solarkennedy/epaper-watch/Ubuntu_B7pt7b.h

const uint8_t Ubuntu_B7pt7bBitmaps[] PROGMEM = {
  0xFF, 0xF3, 0xF0, 0xDE, 0xF7, 0xB0, 0x1B, 0x0D, 0xBF, 0xFF, 0xF3, 0x61,
  0xB3, 0xFF, 0xFF, 0x6C, 0x36, 0x00, 0x30, 0xC7, 0xFF, 0xC3, 0x87, 0x87,
  0x0F, 0xFF, 0x8C, 0x30, 0x78, 0xCC, 0xD8, 0xCF, 0x8C, 0xF0, 0x7E, 0x00,
  0x7E, 0x0F, 0x31, 0xF3, 0x1B, 0x33, 0x1E, 0x38, 0x3E, 0x1B, 0x0D, 0x87,
  0x87, 0xDB, 0x3D, 0x9C, 0xFF, 0x3D, 0xC0, 0xFF, 0x27, 0x6E, 0xCC, 0xCC,
  0xCC, 0xE6, 0x72, 0x4E, 0x67, 0x33, 0x33, 0x33, 0x76, 0xE4, 0x25, 0x7E,
  0xED, 0xA8, 0x30, 0xCF, 0xFF, 0x30, 0xC0, 0x6D, 0xE0, 0xFF, 0xFF, 0x80,
  0x0C, 0x31, 0x86, 0x18, 0xC3, 0x0C, 0x31, 0x86, 0x18, 0xC3, 0x00, 0x39,
  0xEC, 0xF3, 0xCF, 0x3C, 0xF3, 0x79, 0xE0, 0x1B, 0xFE, 0xB1, 0x8C, 0x63,
  0x18, 0xC0, 0x7B, 0xF4, 0xC3, 0x18, 0xE7, 0x38, 0xFF, 0xF0, 0x7B, 0xF0,
  0xC3, 0x38, 0xF0, 0xC3, 0xFF, 0xE0, 0x0C, 0x38, 0xF3, 0x66, 0xD9, 0xBF,
  0xFF, 0x0C, 0x18, 0x7D, 0xF6, 0x18, 0xFB, 0xF0, 0xC3, 0xFF, 0xE0, 0x19,
  0xE6, 0x38, 0xFB, 0xFC, 0xF3, 0x7D, 0xE0, 0xFF, 0xF0, 0x86, 0x10, 0xC3,
  0x18, 0x61, 0x80, 0x7B, 0xFC, 0xF3, 0x7B, 0xFC, 0xF3, 0xFD, 0xE0, 0x7B,
  0xEC, 0xF3, 0xFD, 0xF0, 0xC6, 0x79, 0xC0, 0xFF, 0x81, 0xFF, 0x77, 0x70,
  0x00, 0x66, 0x6C, 0x04, 0x7B, 0xE6, 0x0F, 0x87, 0x81, 0x00, 0xFF, 0xFC,
  0x07, 0xFF, 0xE0, 0x40, 0xF0, 0xF8, 0x33, 0xEF, 0x10, 0x00, 0xFB, 0xF0,
  0xC3, 0x18, 0xC3, 0x00, 0x71, 0xC7, 0x00, 0x0F, 0x83, 0xFE, 0x70, 0xEE,
  0xF3, 0xDF, 0x3D, 0xB3, 0xDB, 0x3D, 0xFE, 0xEF, 0xC7, 0x00, 0x3F, 0x80,
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
  {   277,   7,  10,   8,    1,   -9 },   // 0x46 'F'
  {   286,   8,  10,  10,    1,   -9 },   // 0x47 'G'
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

const GFXfont Ubuntu_B7pt7b PROGMEM = {
  (uint8_t  *)Ubuntu_B7pt7bBitmaps,
  (GFXglyph *)Ubuntu_B7pt7bGlyphs,
  0x20, 0x7E, 16 };

// Approx. 1406 bytes
